KoKoLates/field-robot-2022/assets/images/front_side_v1_01.jpg

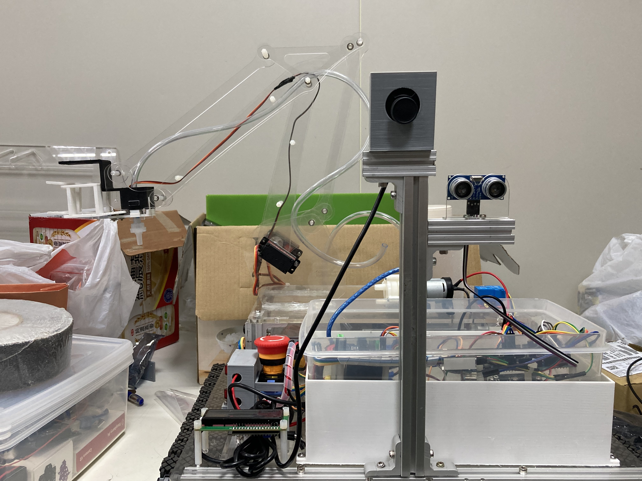
assets/images/front_side_v1_01.jpg
