KoKoLates/field-robot-2022/assets/images/left_side_v2_02.jpg

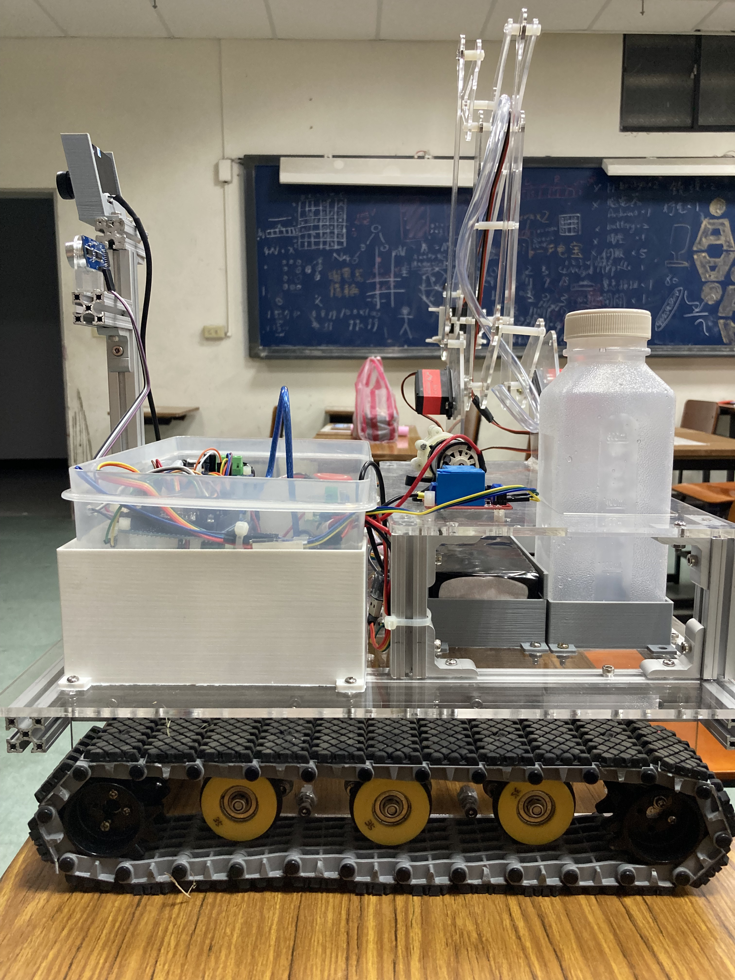
assets/images/left_side_v2_02.jpg
