KoKoLates/field-robot-2022/assets/images/left_side_v2_03.JPG

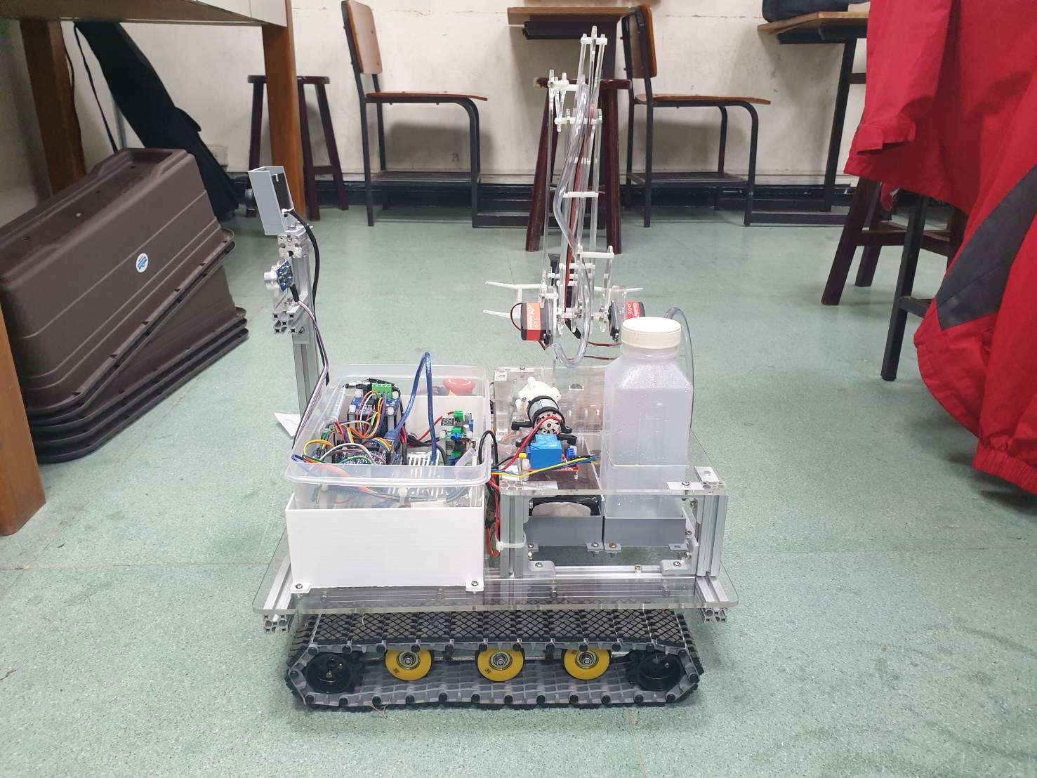
assets/images/left_side_v2_03.JPG
