KoKoLates/field-robot-2022/assets/images/left_side_v2_04.JPG

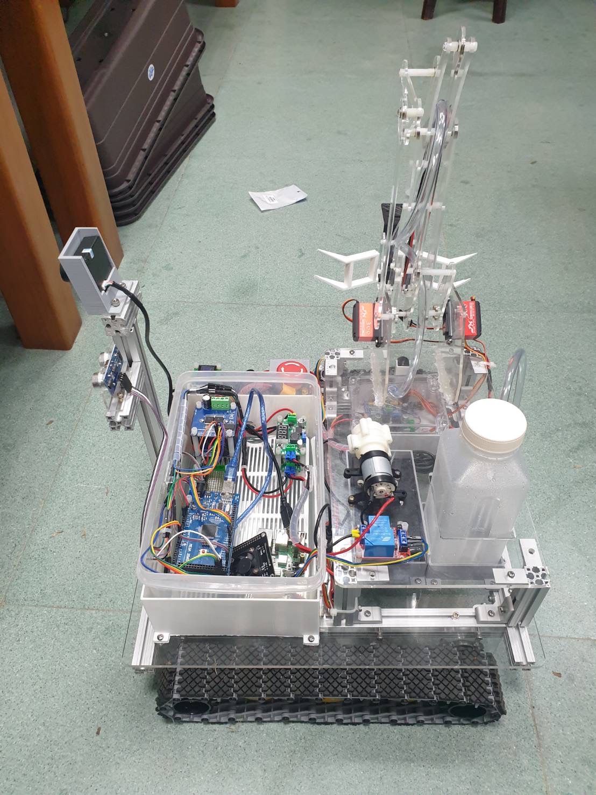
assets/images/left_side_v2_04.JPG
