KoKoLates/field-robot-2022/assets/images/right_side_v2_01.jpg

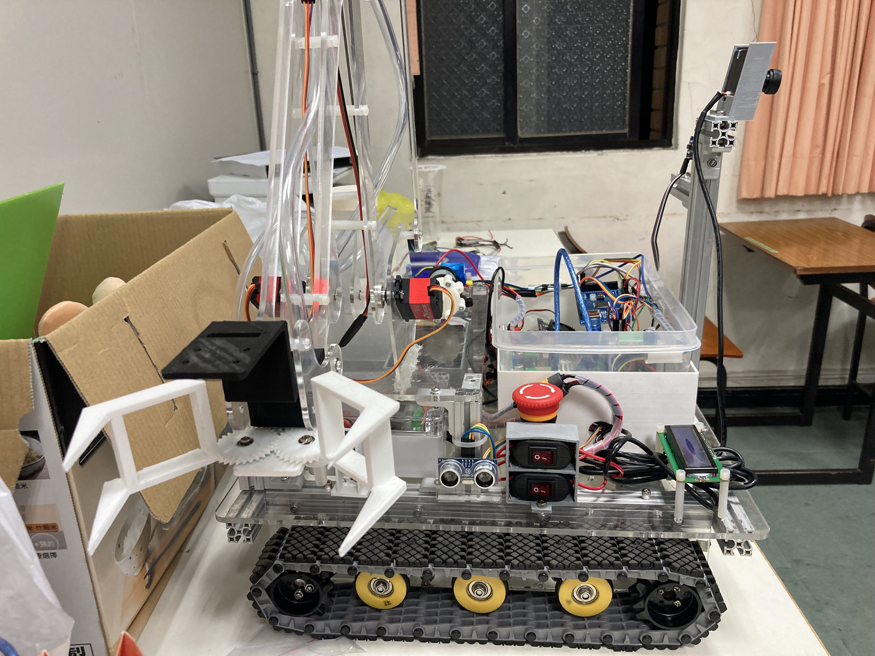
assets/images/right_side_v2_01.jpg
