KoKoLates/field-robot-2022/assets/images/right_side_v2_02.JPG

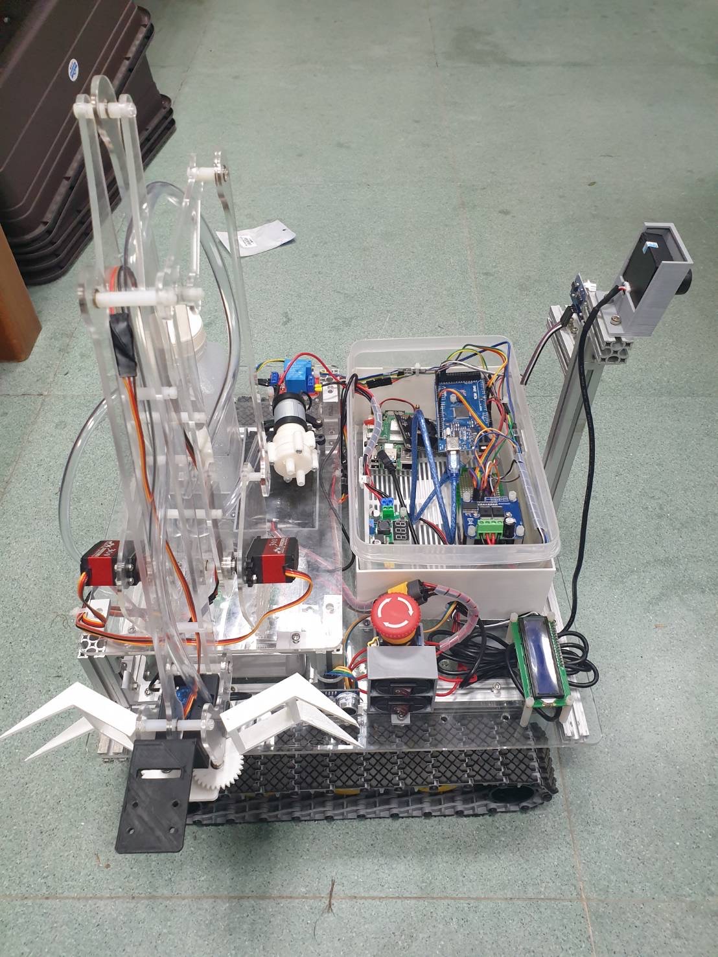
assets/images/right_side_v2_02.JPG
