KoKoLates/field-robot-2022/assets/resources/bear_01.JPG

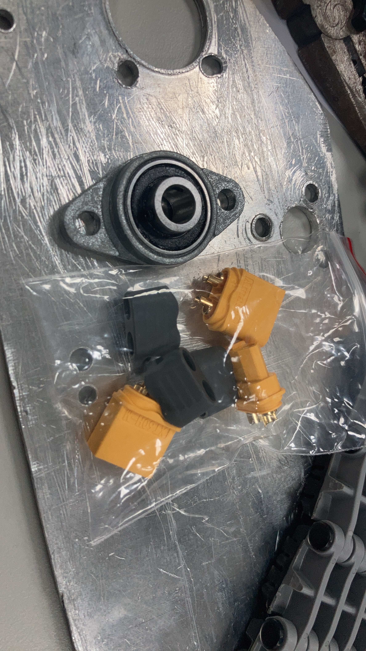
assets/resources/bear_01.JPG
