KoKoLates/field-robot-2022/assets/resources/DBH1(HBridge)_01.png

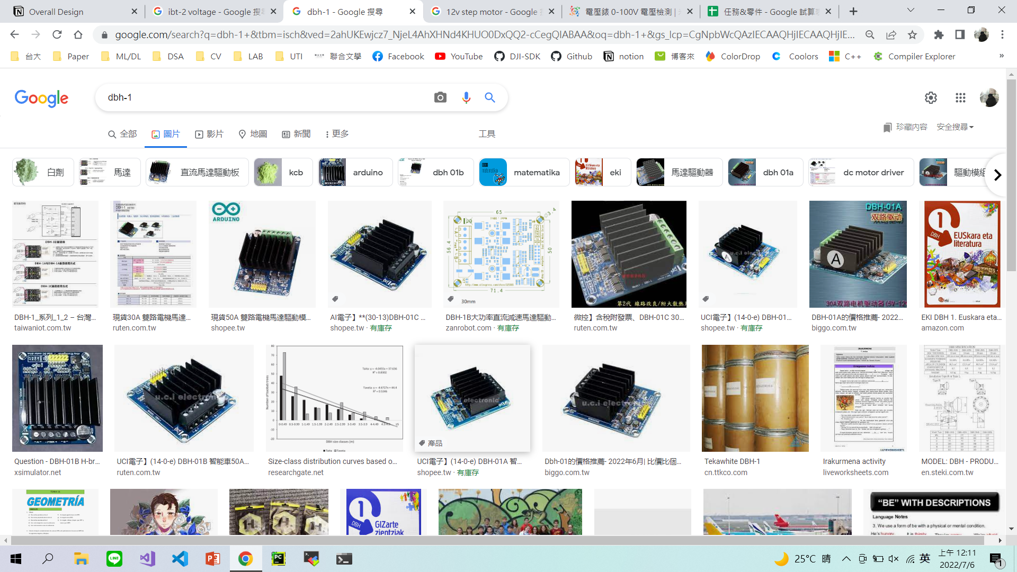
assets/resources/DBH1(HBridge)_01.png
