KoKoLates/field-robot-2022/assets/resources/IBT2_01.png

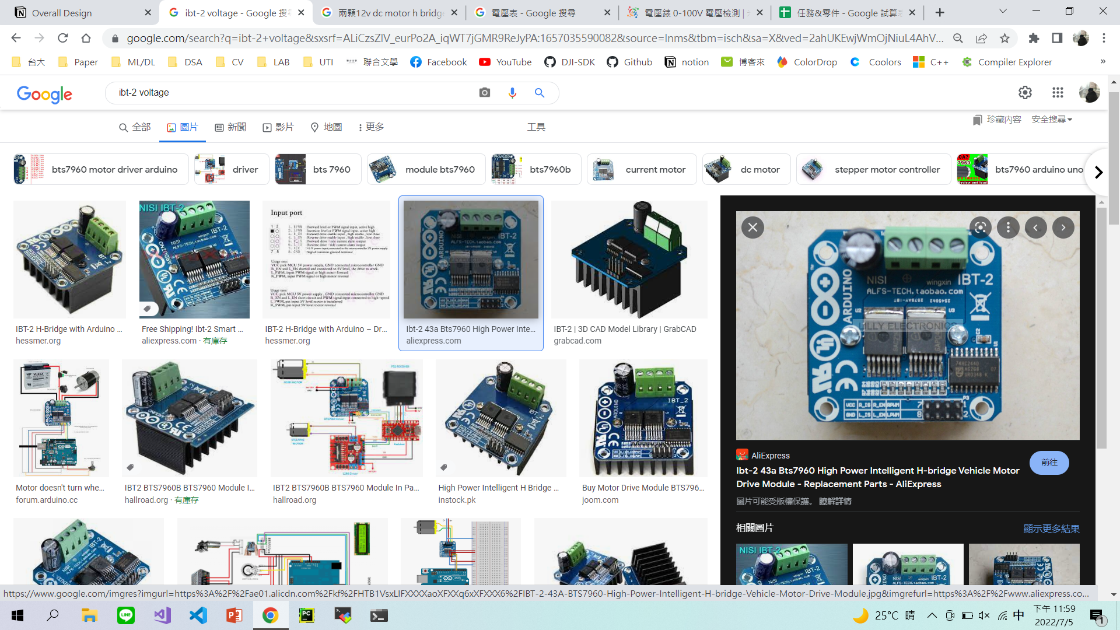
assets/resources/IBT2_01.png
