KoKoLates/field-robot-2022/assets/resources/MOLEX_3.96_2p_connector.jpg

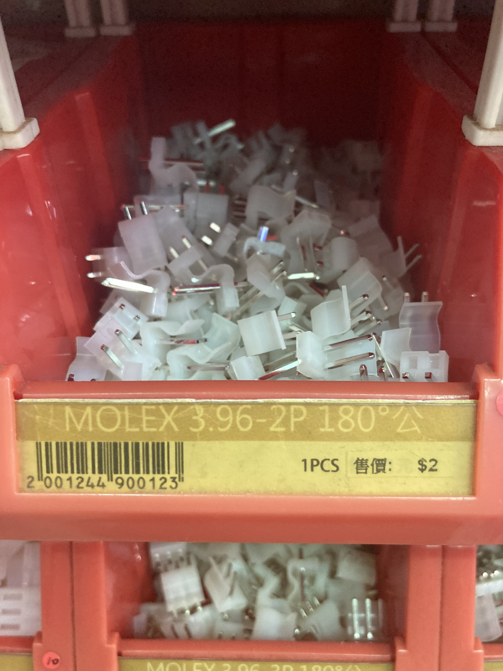
assets/resources/MOLEX_3.96_2p_connector.jpg
