KoKoLates/field-robot-2022/assets/resources/pi_cam_01.JPG

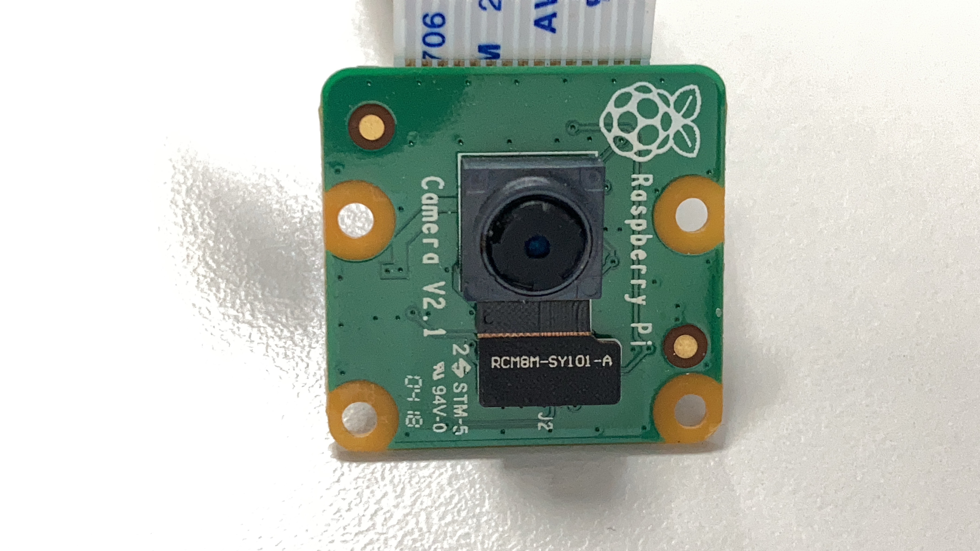
assets/resources/pi_cam_01.JPG
