KoKoLates/field-robot-2022/assets/resources/servo_chip_01.jpg

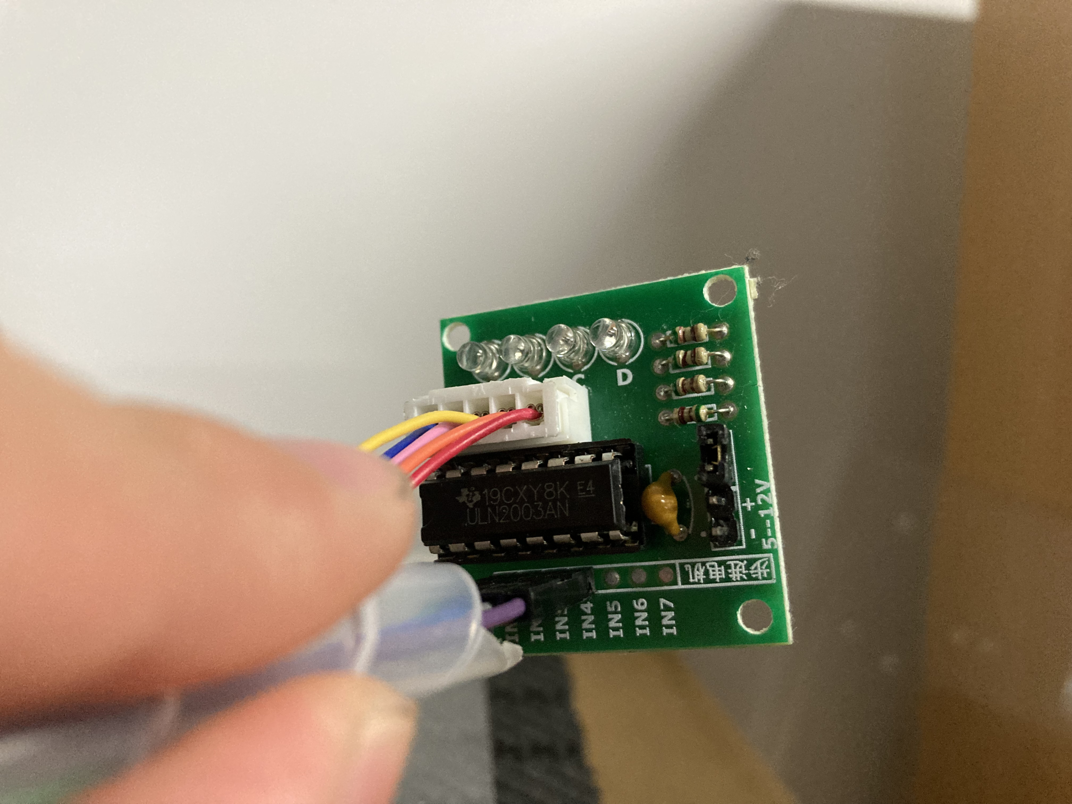
assets/resources/servo_chip_01.jpg
