KoKoLates/field-robot-2022/assets/resources/voltage_display_01.png

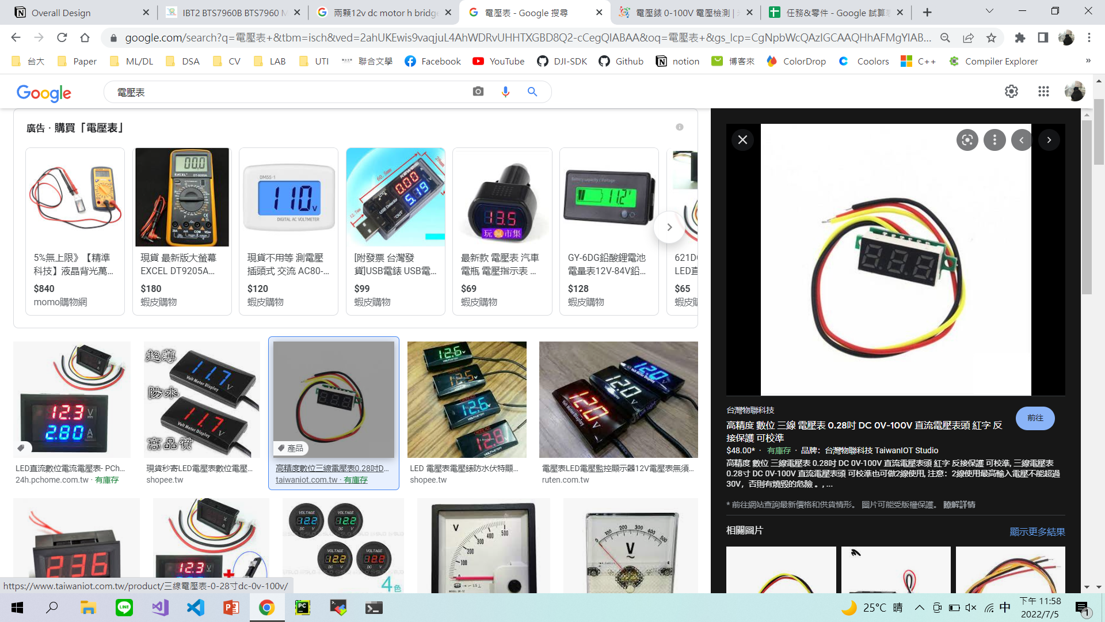
assets/resources/voltage_display_01.png
