KoKoLates/field-robot-2022/assets/resources/voltage_transformer.jpg

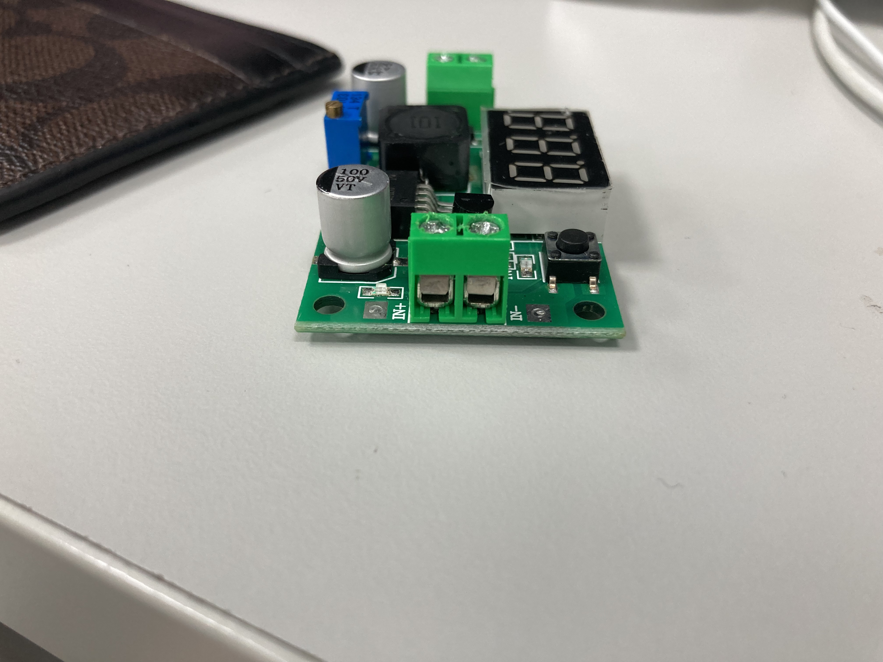
assets/resources/voltage_transformer.jpg
