KoKoLates/field-robot-2022/assets/resources/water_proof_box_01.png

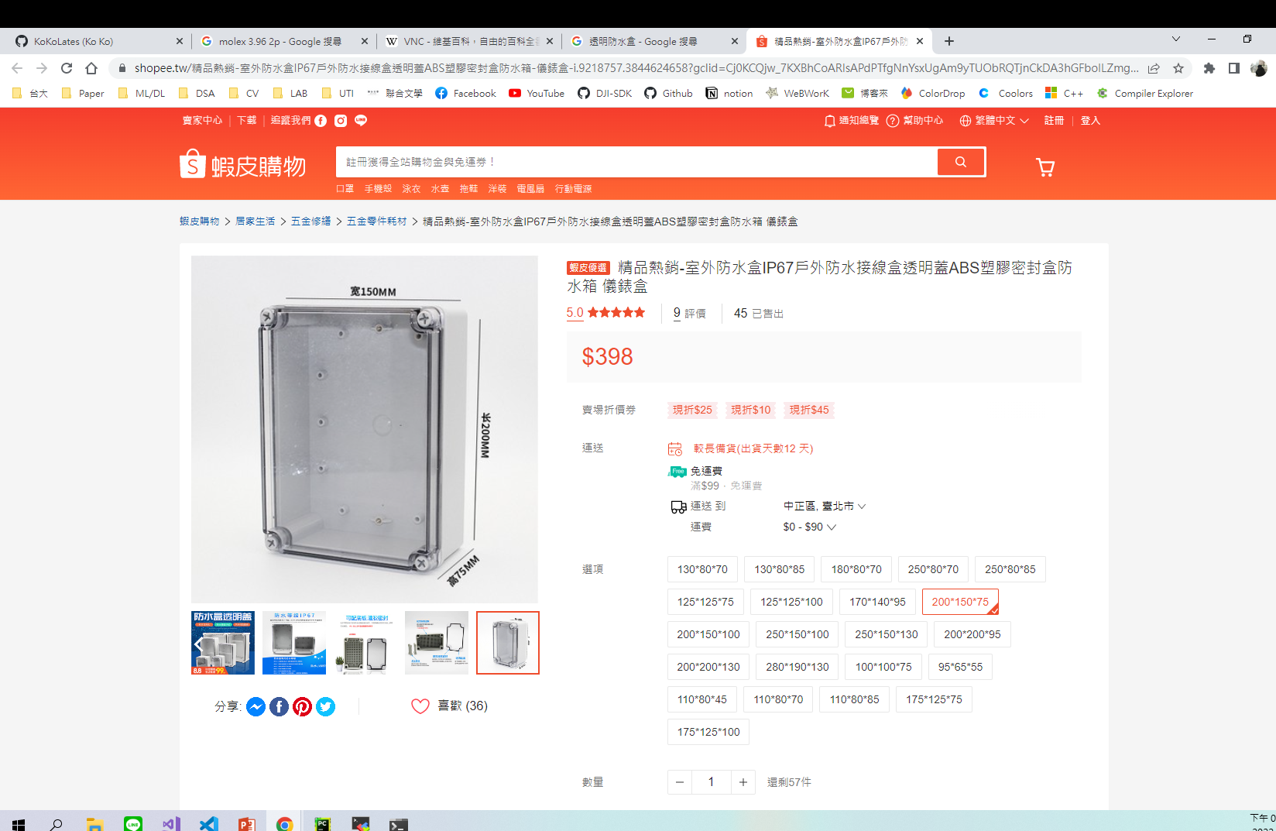
assets/resources/water_proof_box_01.png
