KoKoLates/field-robot-2022/assets/resources/wire_01.JPG

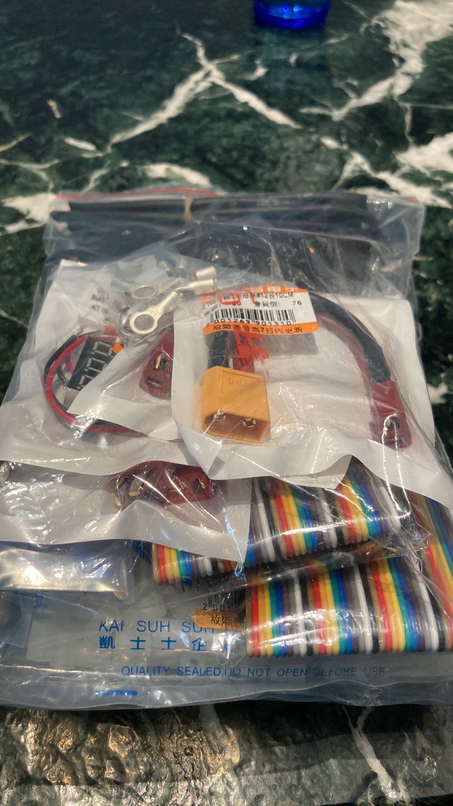
assets/resources/wire_01.JPG
