KoKoLates/field-robot-2022/assets/resources/XT60_connector_01.JPG

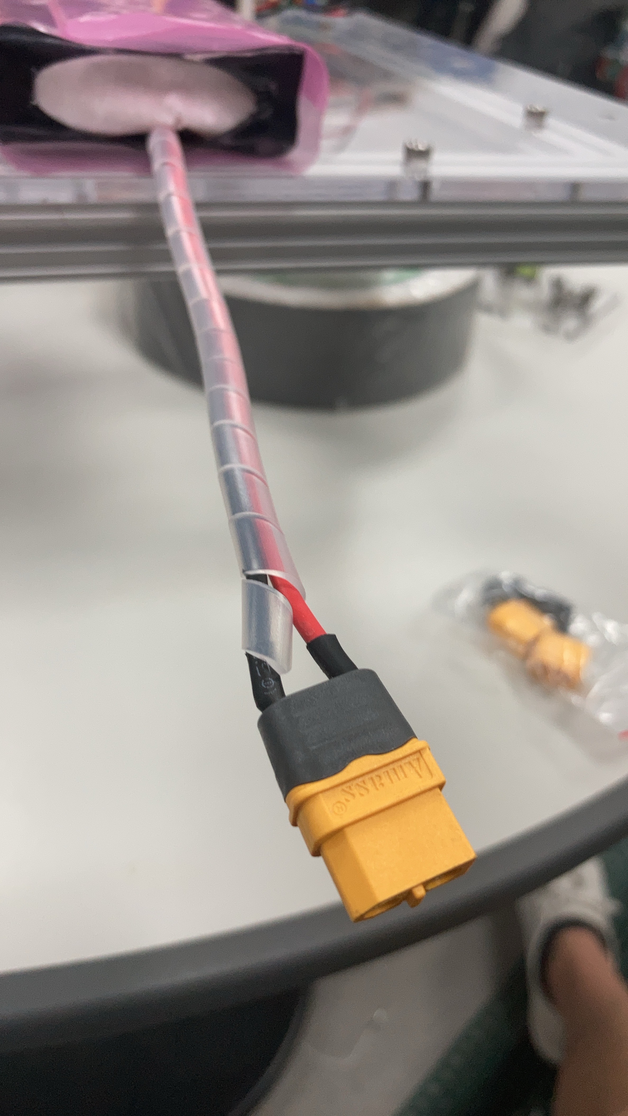
assets/resources/XT60_connector_01.JPG
