KoKoLates/field-robot-2022/circuit/images/circuit_03.JPG

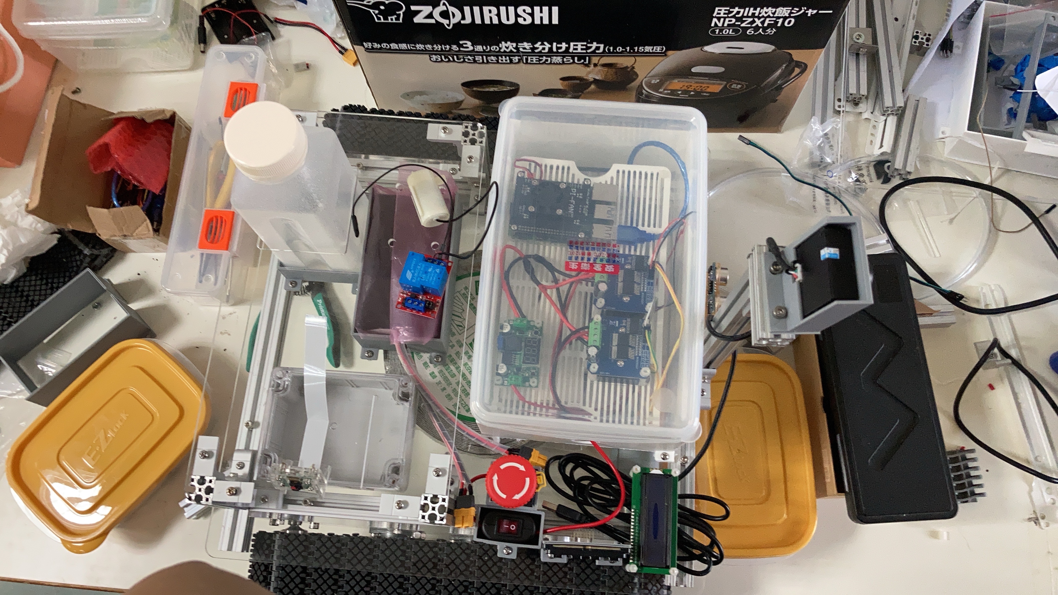
circuit/images/circuit_03.JPG
