KoKoLates/field-robot-2022/circuit/images/circuit_06.jpg

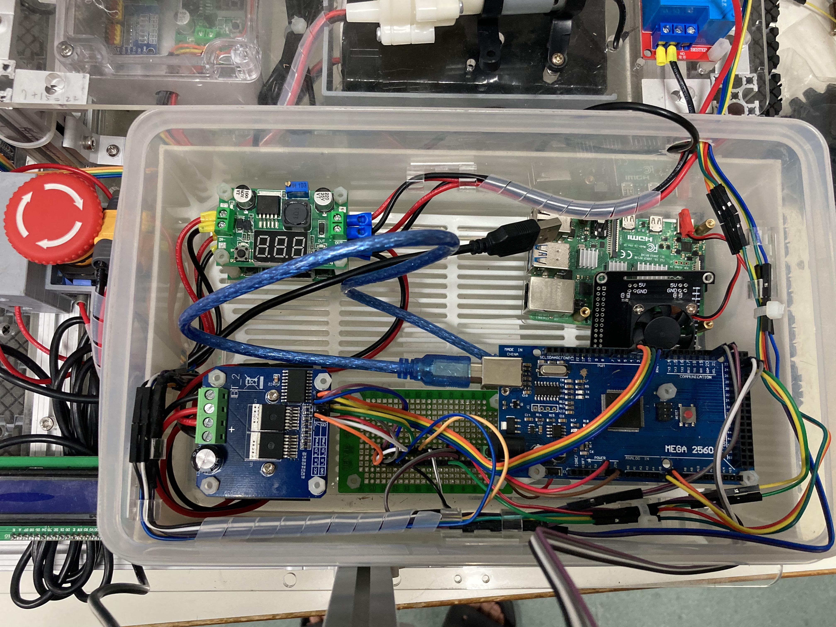
circuit/images/circuit_06.jpg
