KoKoLates/field-robot-2022/circuit/images/circuit_08.jpg

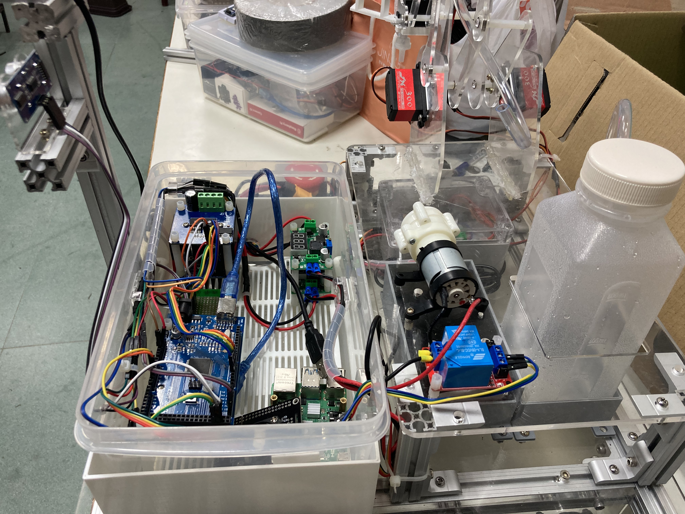
circuit/images/circuit_08.jpg
