KoKoLates/field-robot-2022/robotic_arm/images/arm_02.JPG

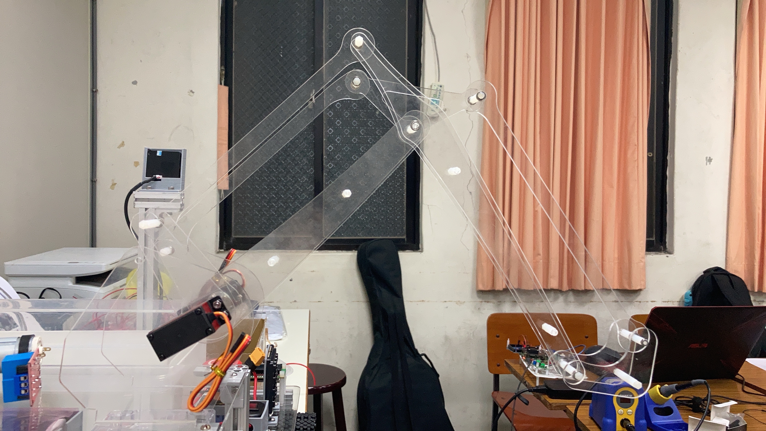
robotic_arm/images/arm_02.JPG
