KoKoLates/field-robot-2022/robotic_arm/images/arm_03.jpg

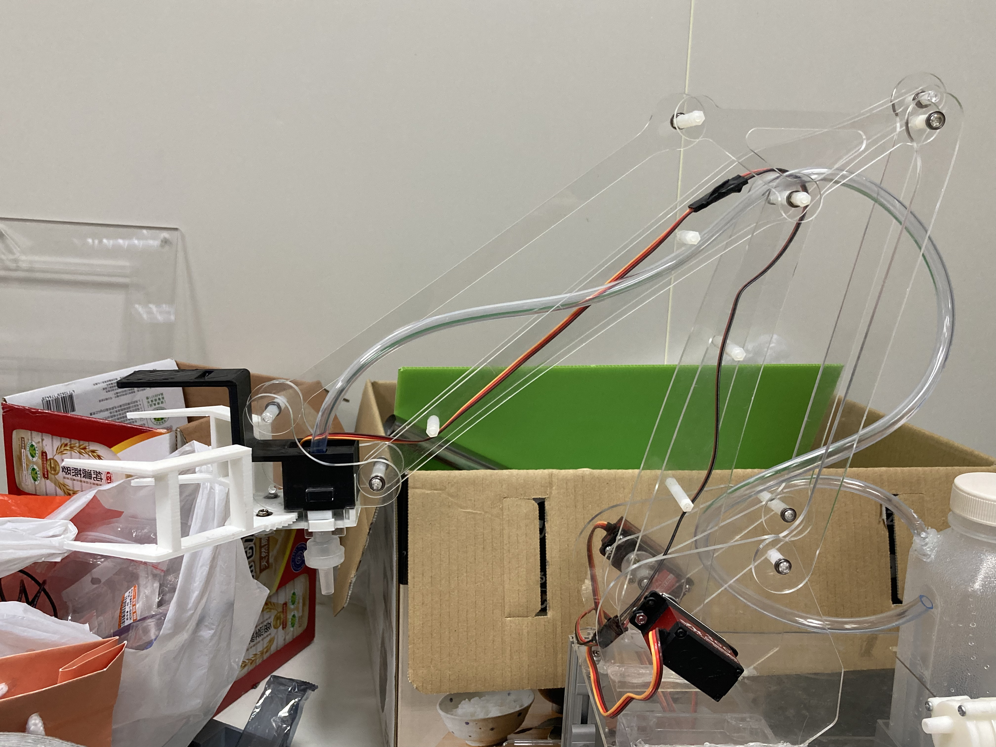
robotic_arm/images/arm_03.jpg
