KoKoLates/field-robot-2022/robotic_arm/images/arm_04.jpg

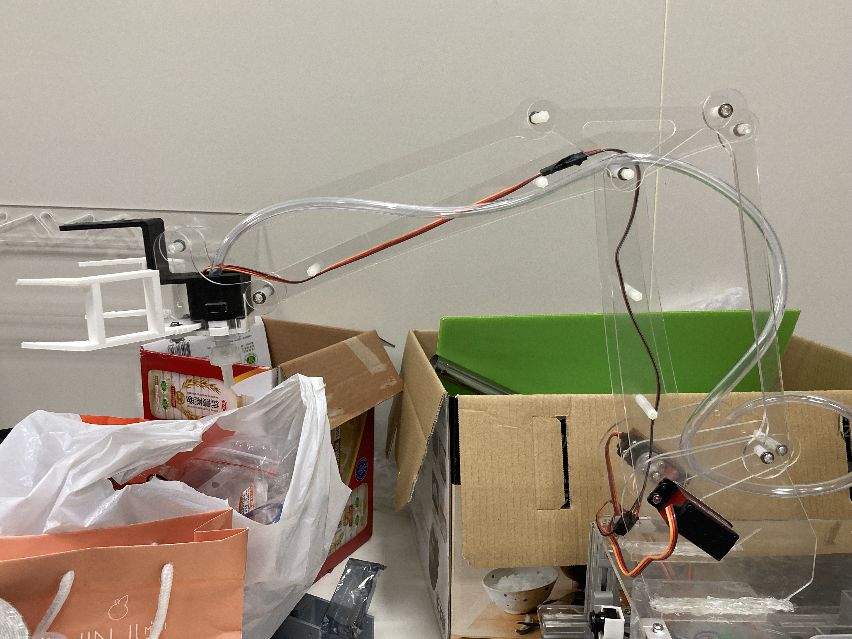
robotic_arm/images/arm_04.jpg
