KoKoLates/field-robot-2022/robotic_arm/images/control_center_02.jpg

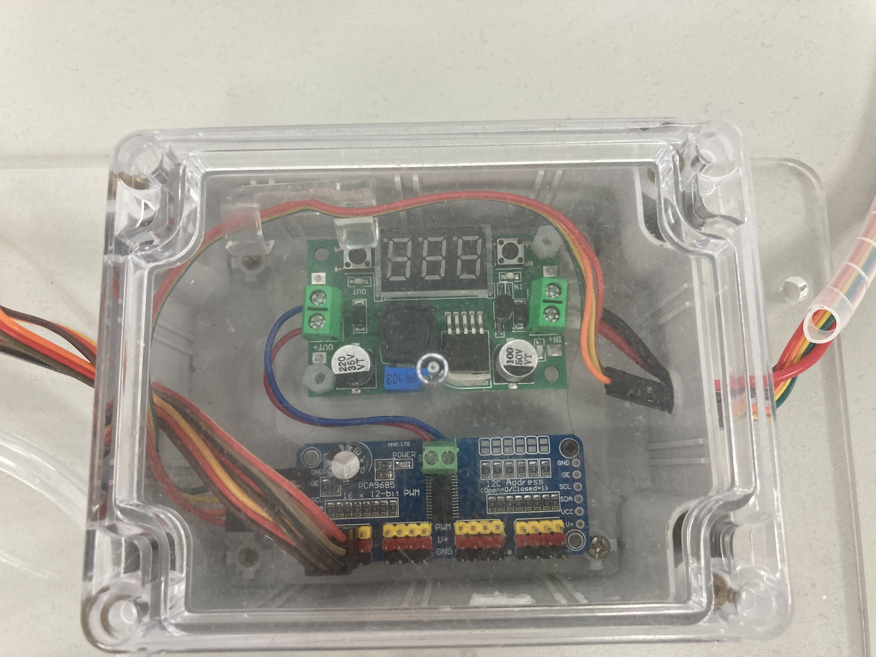
robotic_arm/images/control_center_02.jpg
