KoKoLates/field-robot-2022/robotic_arm/images/gripper_02.jpg

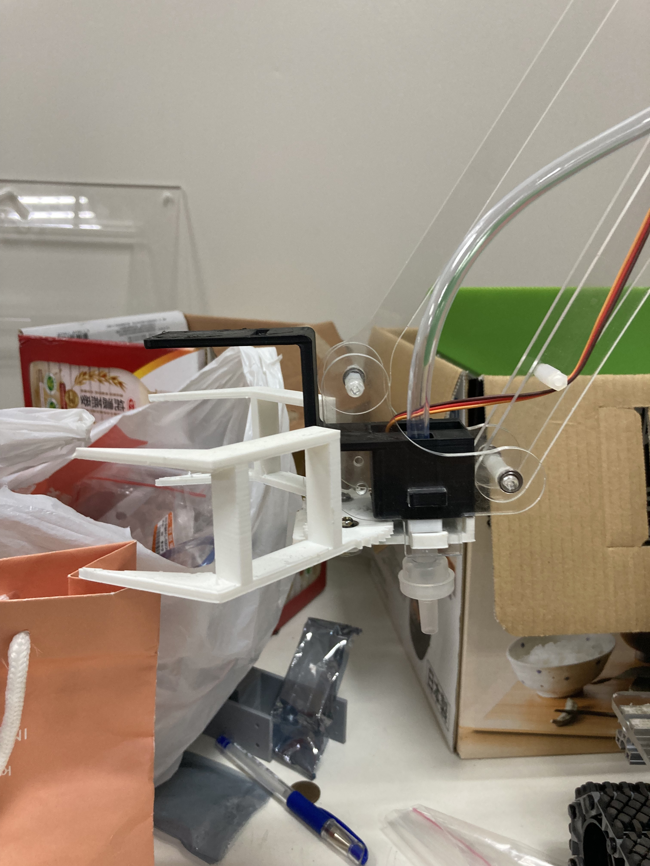
robotic_arm/images/gripper_02.jpg
