KoKoLates/field-robot-2022/robotic_cart/images/bottom_01.jpg

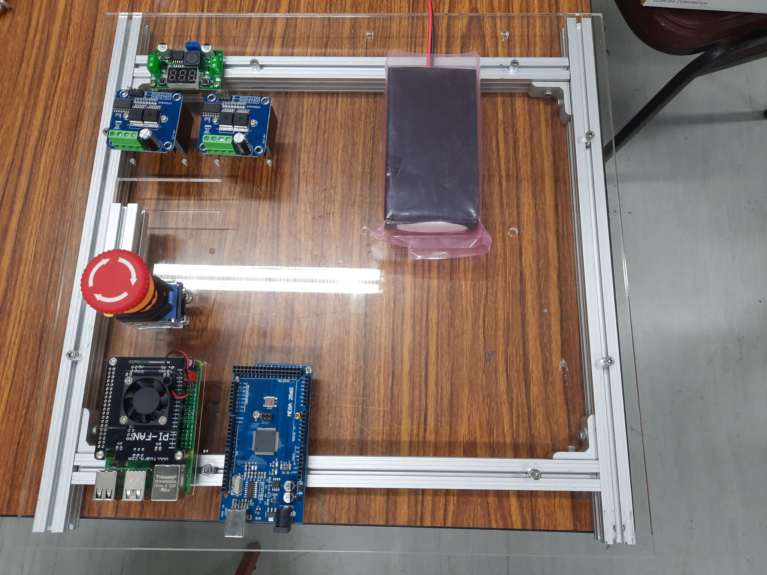
robotic_cart/images/bottom_01.jpg
