KoKoLates/field-robot-2022/robotic_cart/images/bottom_02.JPG

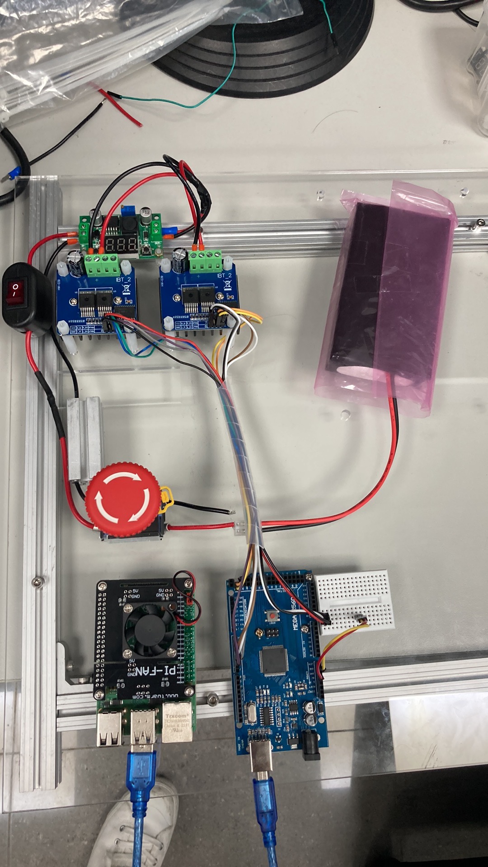
robotic_cart/images/bottom_02.JPG
