KoKoLates/field-robot-2022/robotic_cart/images/bottom_03.JPG

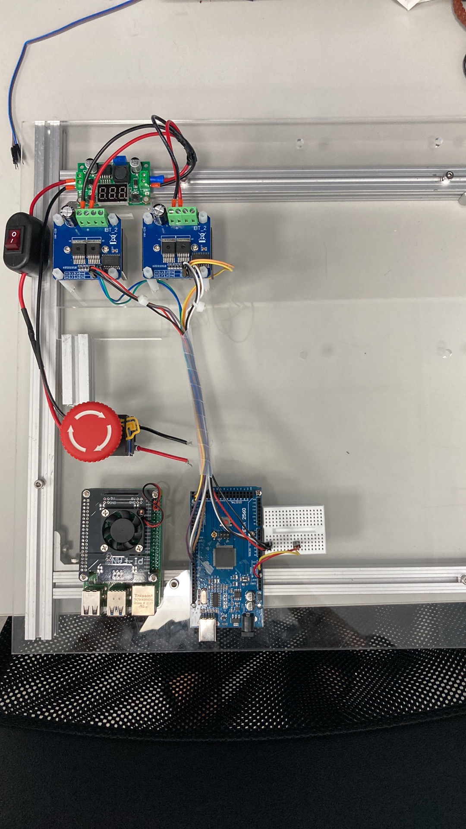
robotic_cart/images/bottom_03.JPG
