KoKoLates/field-robot-2022/robotic_cart/images/side_01.jpg

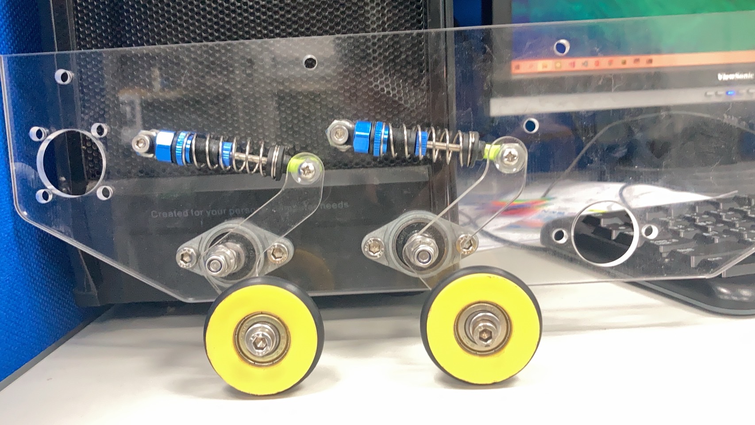
robotic_cart/images/side_01.jpg
