KoKoLates/field-robot-2022/robotic_cart/images/side_03.JPG

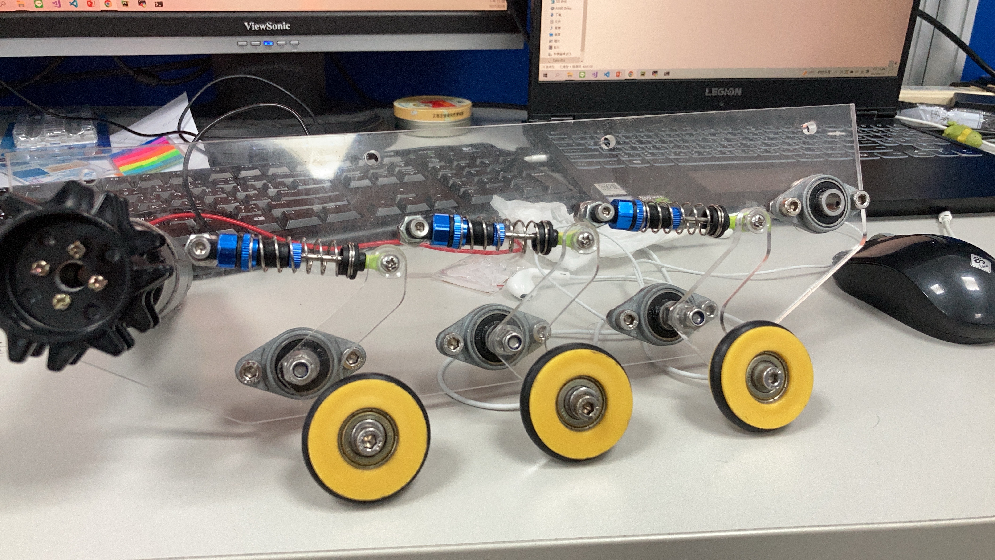
robotic_cart/images/side_03.JPG
