KoKoLates/field-robot-2022/robotic_cart/images/side_cad_01.JPG

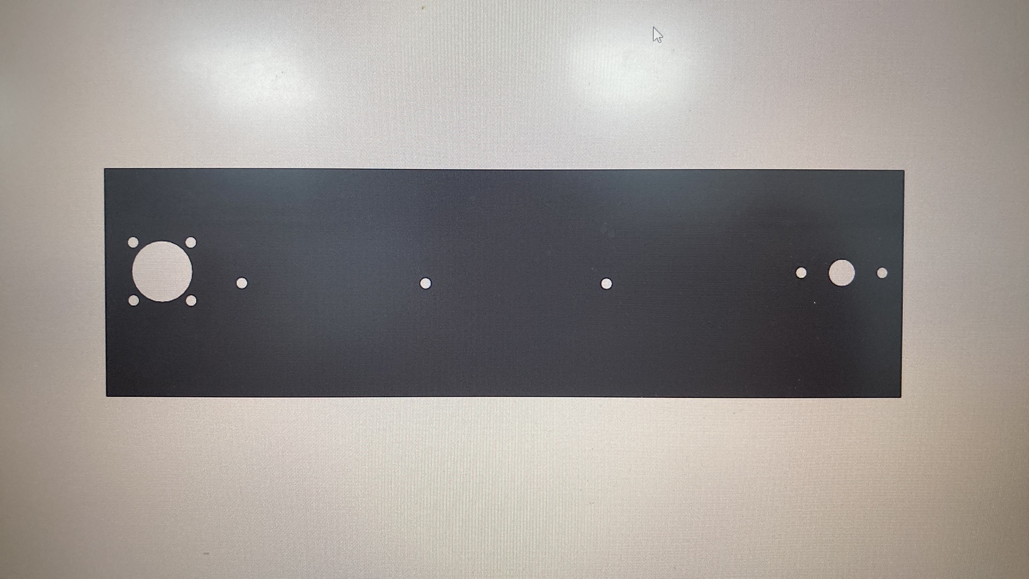
robotic_cart/images/side_cad_01.JPG
