KoKoLates/field-robot-2022/robotic_cart/images/switch_01.JPG

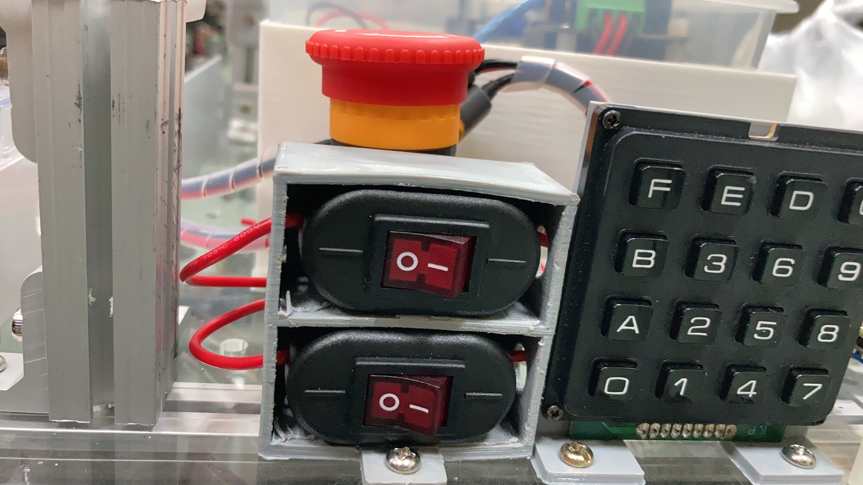
robotic_cart/images/switch_01.JPG
