KoKoLates/field-robot-2022/robotic_arm/hardware/arm4.SLDPRT

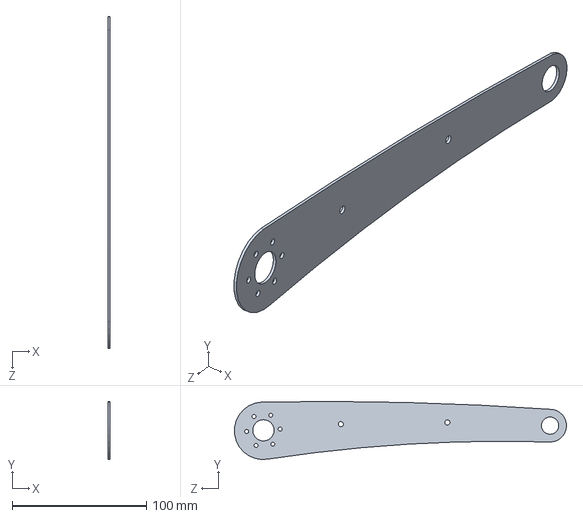
[picture p82: CAD file, 2022-10-20]
robotic_arm/hardware/arm4.SLDPRT
1.50 x 43.3 x 247.5 mm
