KoKoLates/field-robot-2022/robotic_arm/hardware/arm1.SLDPRT

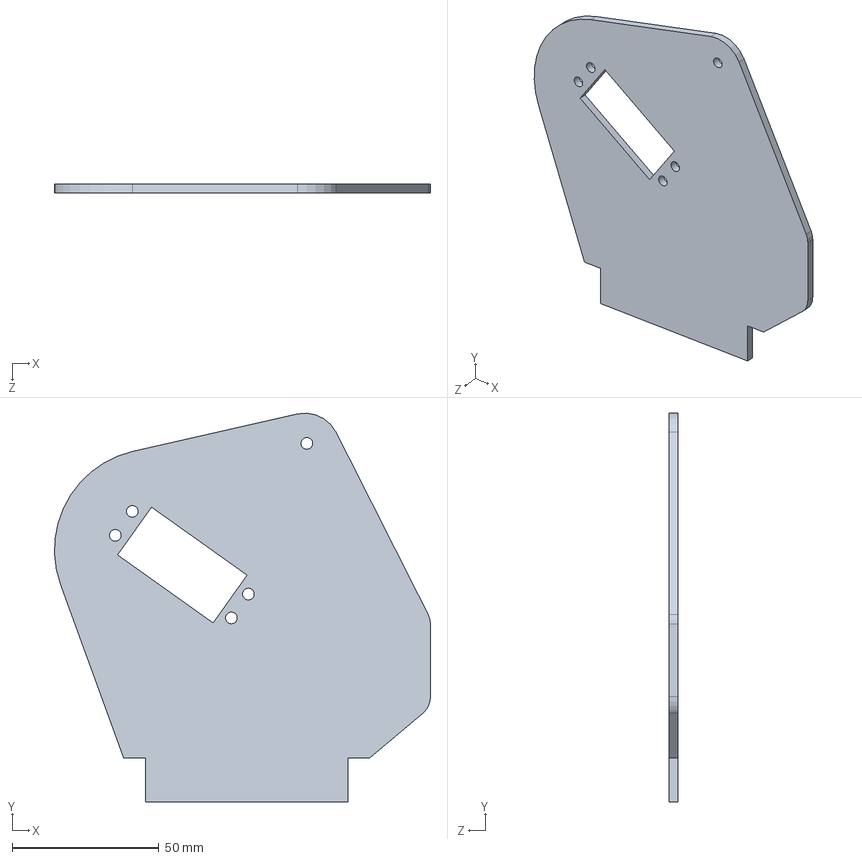
[picture p83: CAD file, 2022-10-20]
robotic_arm/hardware/arm1.SLDPRT
128.2 x 132.5 x 3.00 mm
