KoKoLates/field-robot-2022/robotic_arm/hardware/arm8.SLDPRT

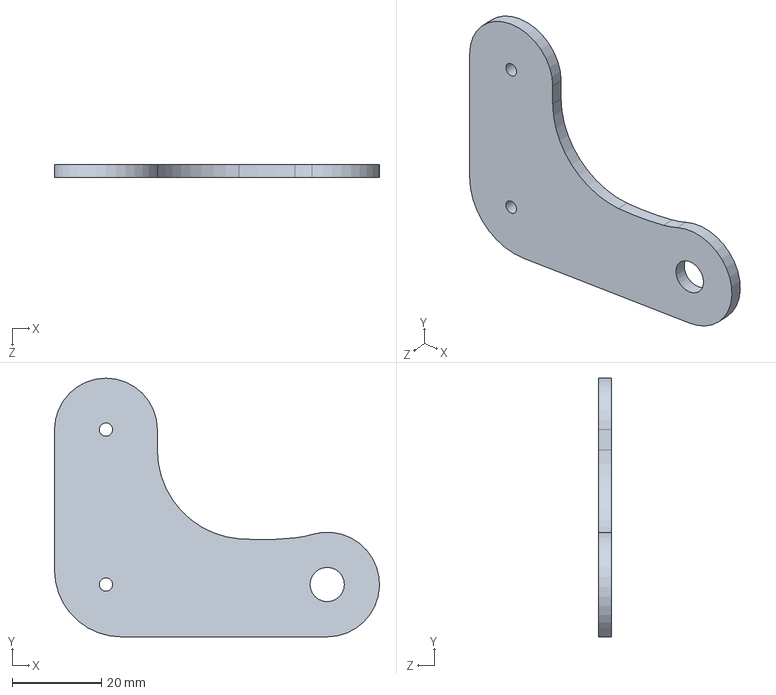
[picture p84: CAD file, 2022-10-20]
robotic_arm/hardware/arm8.SLDPRT
73.0 x 58.1 x 3.00 mm
