KoKoLates/field-robot-2022/robotic_arm/hardware/arm5_back.SLDPRT

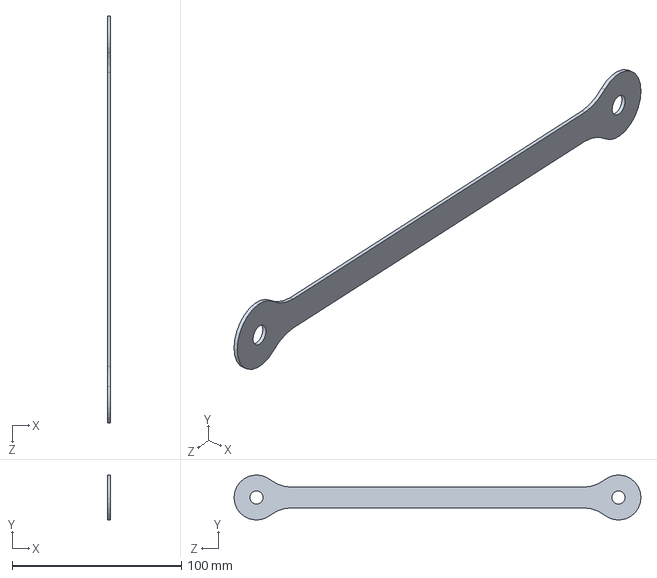
[picture p85: CAD file, 2022-10-20]
robotic_arm/hardware/arm5_back.SLDPRT
1.50 x 26.5 x 240.4 mm
