KoKoLates/field-robot-2022/robotic_arm/hardware/483_bear.SLDPRT

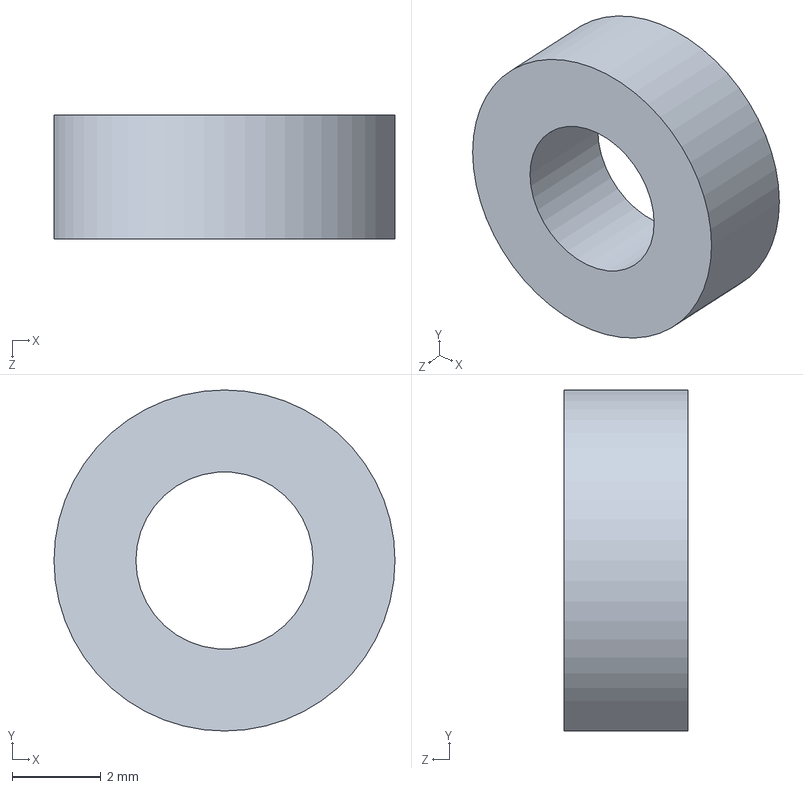
[picture p86: CAD file, 2022-10-20]
robotic_arm/hardware/483_bear.SLDPRT
7.70 x 7.70 x 2.80 mm
