KoKoLates/field-robot-2022/circuit/images/circuit_04.JPG

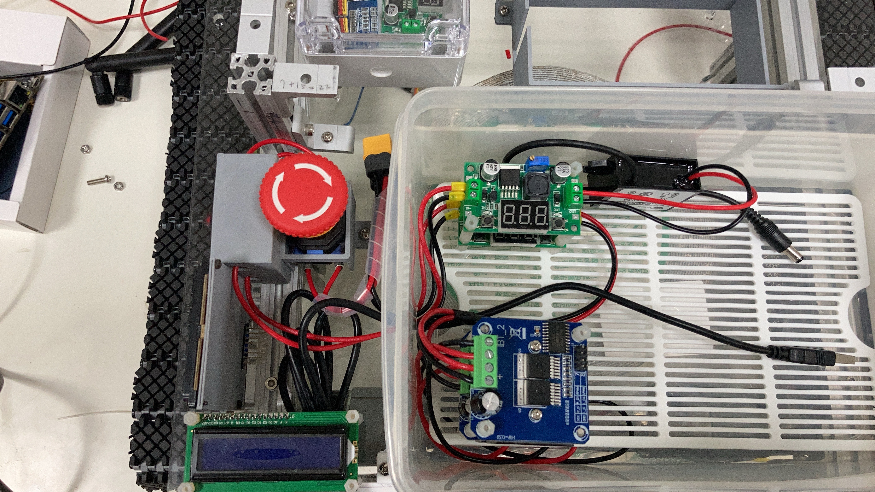
circuit/images/circuit_04.JPG
